jaapgeurts/sunkbdadapter/firmware/sun_type6_adapter.X/sunkeytable.h

#ifndef _SUN_KEYTABLE_H
#define _SUN_KEYTABLE_H

unsigned char keytable[] = {
    /* 0 */  0x00,
    /* 1 */  0x78, // stop
    /* 2 */  0x81, // volume down
    /* 3 */  0x79, // again
    /* 4 */  0x80, // volume up
    /* 5 */  0x3a, // F1
    /* 6 */  0x3b, // F2
    /* 7 */  0x43, // F10
    /* 8 */  0x3c, // F3
    /* 9 */  0x44, // F11
    /* 10 */ 0x3d, // F4
    /* 11 */ 0x45, // F12
    /* 12 */ 0x3e, // F5
    /* 13 */ 0xe6, // r_alt_graph
    /* 14 */ 0x3f, // F6
    /* 15 */ 0x68, // blank (esc pos) = // F13
    /* 16 */ 0x40, // F7
    /* 17 */ 0x41, // F8
    /* 18 */ 0x42, // F9
    /* 19 */ 0xe2, // l_alt
    /* 20 */ 0x52, // up
    /* 21 */ 0x48, // pause
    /* 22 */ 0x46, // prtscr
    /* 23 */ 0x47, // scroll lock
    /* 24 */ 0x50, // left
    /* 25 */ 0x76, // props
    /* 26 */ 0x7a, // undo
    /* 27 */ 0x51, // down
    /* 28 */ 0x4f, // right
    /* 29 */ 0x29, // esc
    /* 30 */ 0x1e, // 1
    /* 31 */ 0x1f, // 2
    /* 32 */ 0x20, // 3
    /* 33 */ 0x21, // 4
    /* 34 */ 0x22, // 5
    /* 35 */ 0x23, // 6
    /* 36 */ 0x24, // 7
    /* 37 */ 0x25, // 8
    /* 38 */ 0x26, // 9
    /* 39 */ 0x27, // 0
    /* 40 */ 0x2d, // -
    /* 41 */ 0x2e, // =
    /* 42 */ 0x35, // `
    /* 43 */ 0x2a, // backspace
    /* 44 */ 0x49, // insert
    /* 45 */ 0x7f, // mute
    /* 46 */ 0x54, // num_div
    /* 47 */ 0x55, // num_star
    /* 48 */ 0x66, // power off
    /* 49 */ 0x77, // Front
    /* 50 */ 0x63, // num_.
    /* 51 */ 0x7c, // Copy
    /* 52 */ 0x4a, // home
    /* 53 */ 0x2b, // tab
    /* 54 */ 0x14, // q 
    /* 55 */ 0x1a, // w
    /* 56 */ 0x08, // e
    /* 57 */ 0x15, // r
    /* 58 */ 0x17, // t
    /* 59 */ 0x1c, // y
    /* 60 */ 0x18, // u
    /* 61 */ 0x0c, // i
    /* 62 */ 0x12, // o
    /* 63 */ 0x13, // p
    /* 64 */ 0x2f, // [
    /* 65 */ 0x30, // ]
    /* 66 */ 0x4c, // delete
    /* 67 */ 0x65, // compose
    /* 68 */ 0x5f, // num_7
    /* 69 */ 0x60, // num_8
    /* 70 */ 0x61, // num_9
    /* 71 */ 0x56, // num_min
    /* 72 */ 0x74, // open
    /* 73 */ 0x7d, // paste
    /* 74 */ 0x4d, // end
    /* 75 */ 0x00,
    /* 76 */ 0xe0, // left_control
    /* 77 */ 0x04, // a
    /* 78 */ 0x16, // s
    /* 79 */ 0x07, // d
    /* 80 */ 0x09, // f
    /* 81 */ 0x0a, // g
    /* 82 */ 0x0b, // h
    /* 83 */ 0x0d, // j
    /* 84 */ 0x0e, // k
    /* 85 */ 0x0f, // l
    /* 86 */ 0x33, // ;
    /* 87 */ 0x34, // '
    /* 88 */ 0x31, // backslash
    /* 89 */ 0x28, // return
    /* 90 */ 0x58, // num_enter
    /* 91 */ 0x5c, // num_4
    /* 92 */ 0x5d, // num_5
    /* 93 */ 0x5e, // num_6
    /* 94 */ 0x62, // num_0
    /* 95 */ 0x7e, // find
    /* 96 */ 0x4b, // page up
    /* 97 */  0x7b, // cut
    /* 98 */  0x53, // num_lock
    /* 99 */  0xe1, // l_shift
    /* 100 */ 0x1d, // z 
    /* 101 */ 0x1b, // x
    /* 102 */ 0x06, // c
    /* 103 */ 0x19, // v
    /* 104 */ 0x05, // b
    /* 105 */ 0x11, // n
    /* 106 */ 0x10, // m
    /* 107 */ 0x36, // ,
    /* 108 */ 0x37, // .
    /* 109 */ 0x38, // forwardslash
    /* 110 */ 0xe5, // r_shift
    /* 111 */ 0x00,
    /* 112 */ 0x59, // num_1
    /* 113 */ 0x5a, // num_2
    /* 114 */ 0x5b, // num_3
    /* 115 */ 0x00,
    /* 116 */ 0x00,
    /* 117 */ 0x00,
    /* 118 */ 0x75, // help
    /* 119 */ 0x39, // caps_lock
    /* 120 */ 0xe3, // l_meta
    /* 121 */ 0x2c, // space
    /* 122 */ 0xe7, // r_meta
    /* 123 */ 0x4e, // page down
    /* 124 */ 0x00,
    /* 125 */ 0x57, // num_plus
    /* 126 */ 0x00,
    /* 127 */ 0x00,

};

#endif
